mikeabuilder/solder-fume-extractor/3.2mm material/DXF files/Housing Light Holder.dxf

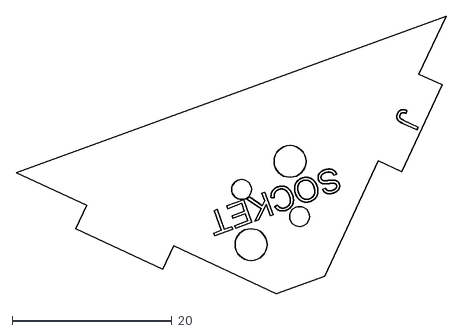
[picture p16: CAD file, 2021-05-19]
3.2mm material/DXF files/Housing Light Holder.dxf
53.8 x 34.8
