mikeabuilder/solder-fume-extractor/3.2mm material/DXF files/Housing Reflector.dxf

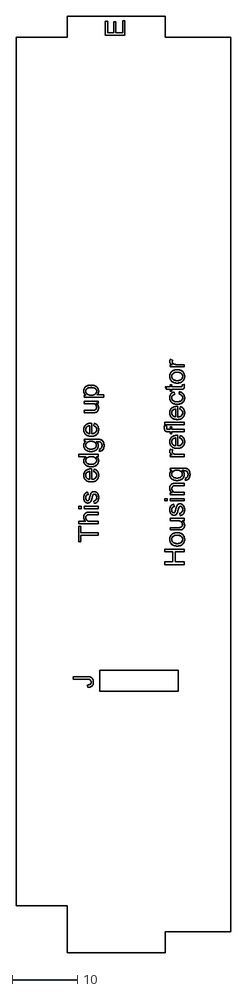
[picture p17: CAD file, 2021-05-19]
3.2mm material/DXF files/Housing Reflector.dxf
32.7 x 143.2
