mikeabuilder/solder-fume-extractor/3.2mm material/DXF files/Housing Hood Front.dxf

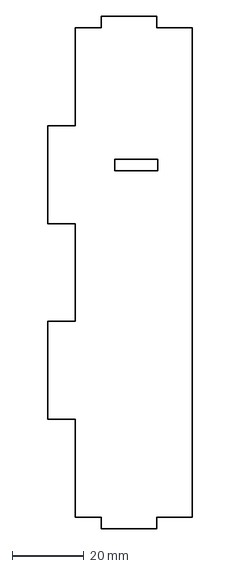
[picture p18: CAD file, 2021-05-09]
3.2mm material/DXF files/Housing Hood Front.dxf
40.5 x 143.2 mm
