mikeabuilder/solder-fume-extractor/3.2mm material/DXF files/Base air deflector.dxf

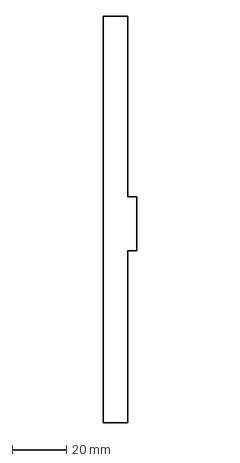
[picture p19: CAD file, 2021-05-09]
3.2mm material/DXF files/Base air deflector.dxf
12.2 x 149.6 mm
