mikeabuilder/solder-fume-extractor/3.2mm material/DXF files/Housing Front.dxf

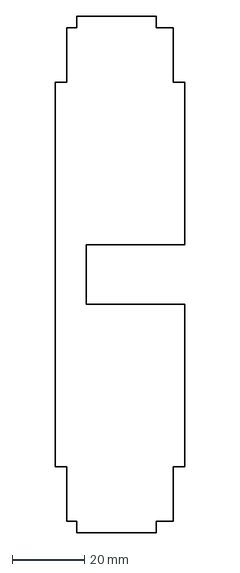
[picture p20: CAD file, 2021-05-09]
3.2mm material/DXF files/Housing Front.dxf
36.0 x 143.2 mm
